Resaj/slot-wheels-heaters/eagle/Wheels heaters/Photolites/Control_PCB_BOTTOM.jpg

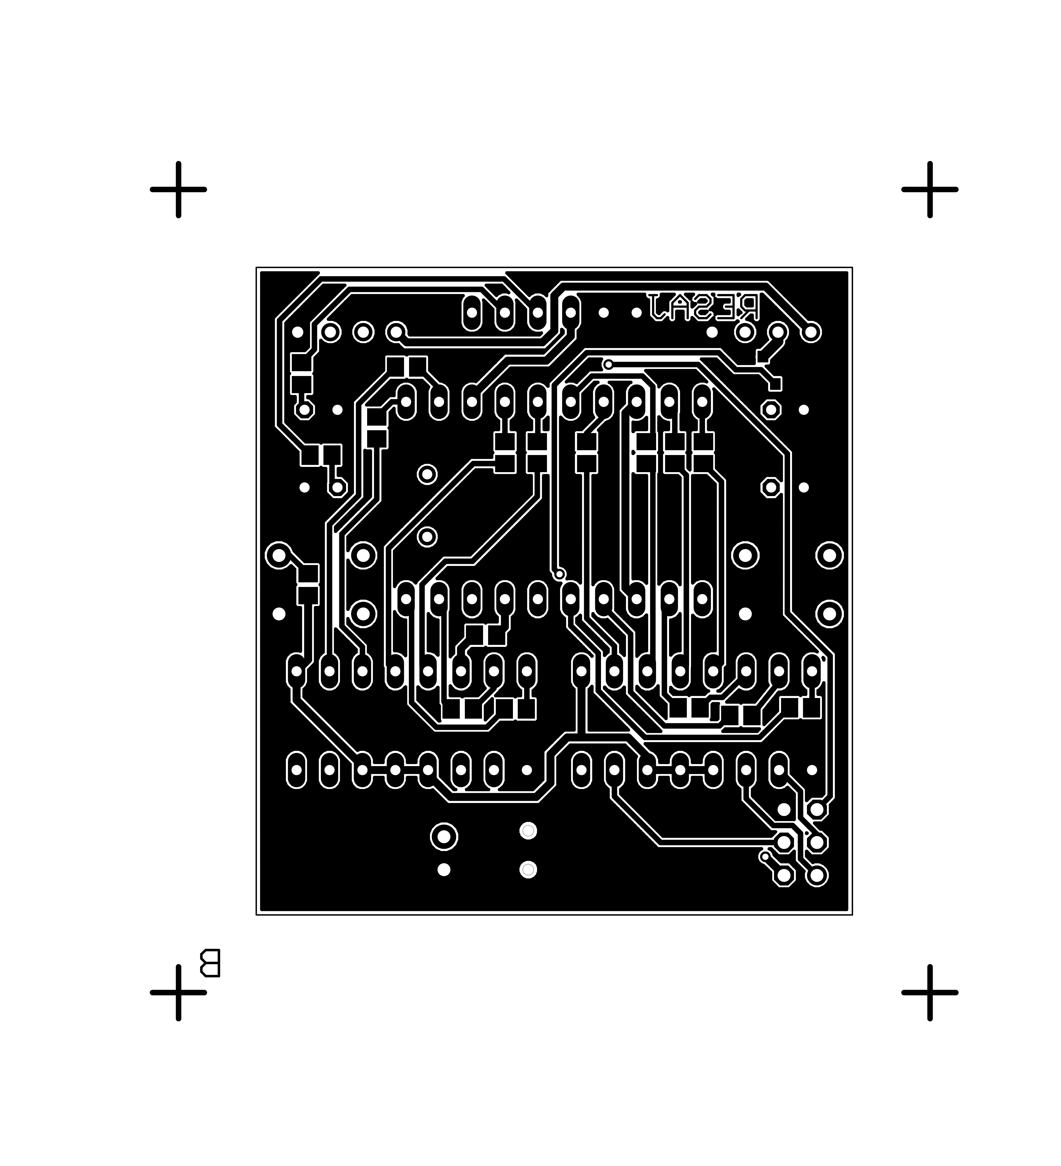
eagle/Wheels heaters/Photolites/Control_PCB_BOTTOM.jpg
